marian163/proiect_tsc/Hardware/Schematic_PCB.sch

## EAGLE design Hardware/Schematic_PCB.sch (2026-04-19)

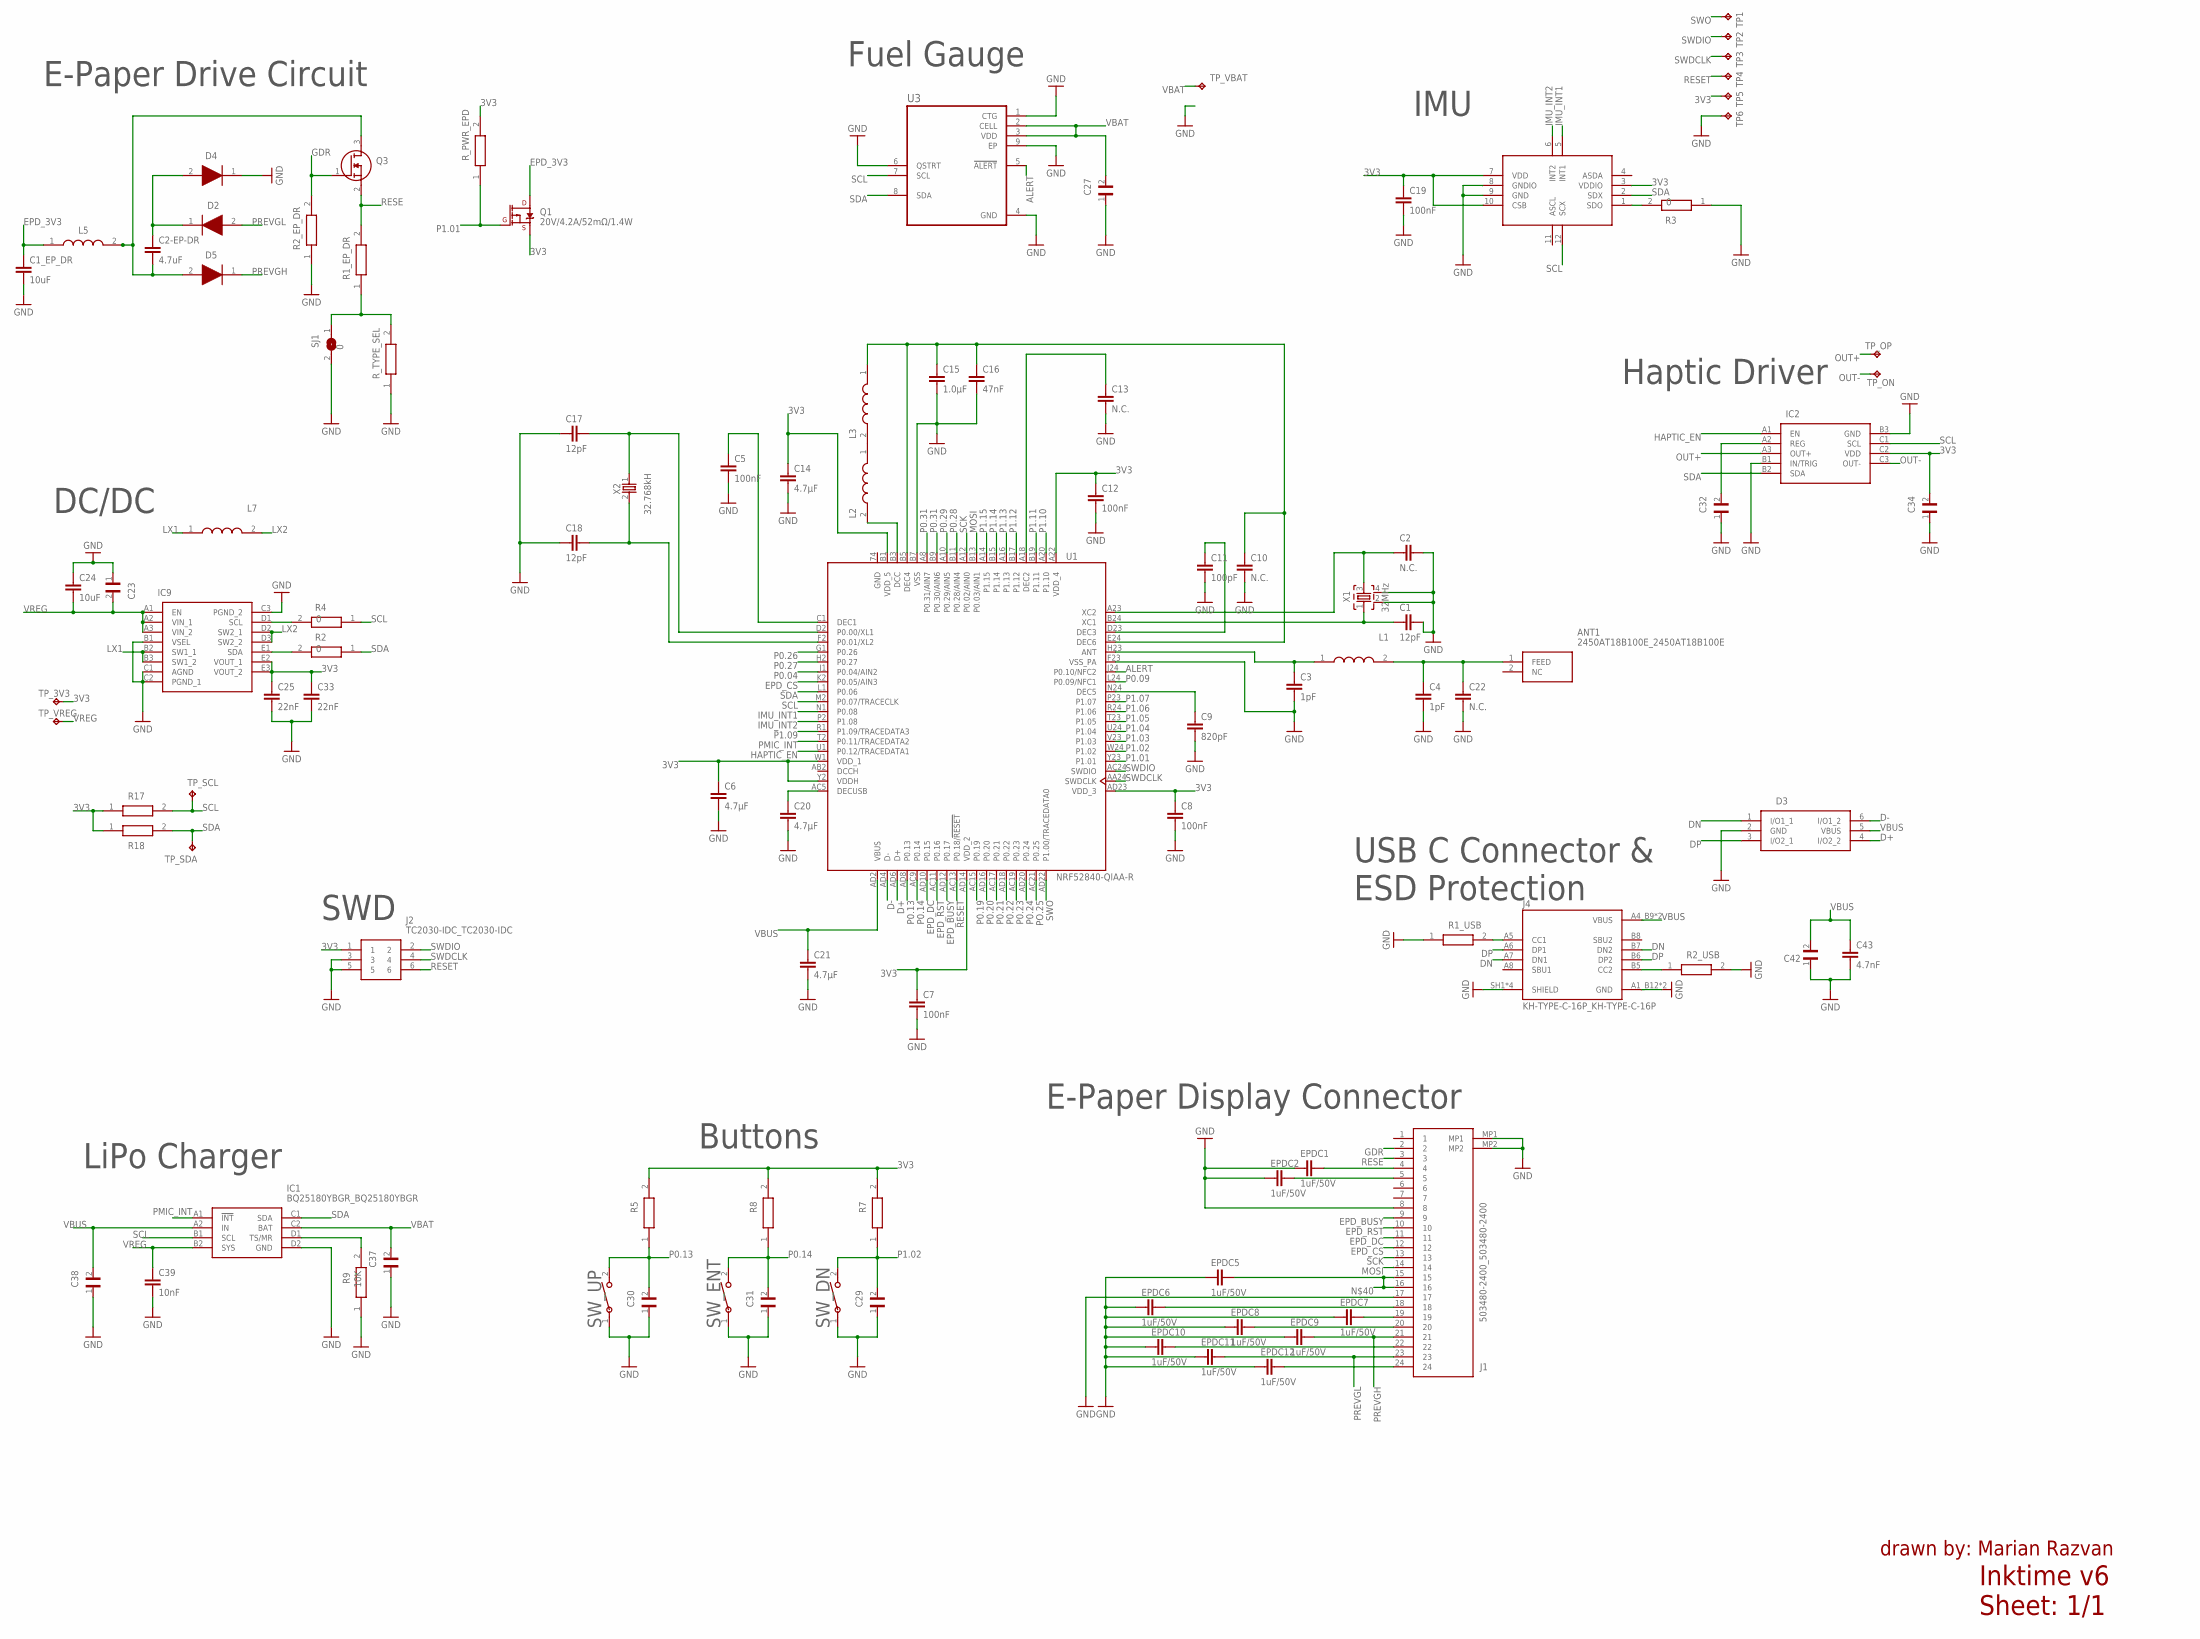
[picture p6: schematic Schematic_PCB.sch, sheet 1]

Parts:
ANT1: 2450AT18B100E_2450AT18B100E; 2450AT18B100E_ANTC3216X140N
C1, C17, C18: 12pF; NORDIC_NRF_3_RESC0201_L
C1_EP_DR, C24: 10uF; NORDIC_NRF_3_RESC0201_L
C2, C10, C13, C22: N.C.; NORDIC_NRF_3_RESC0201_L
C2-EP-DR: 4.7uF; ESP32_C6_LIBRARY_1_ESP32_WROVER_EAGLE-LTSPICE_C0402
C3, C4: 1pF; NORDIC_NRF_3_RESC0201_L
C5, C7, C8, C12, C19: 100nF; NORDIC_NRF_3_RESC0201_L
C6, C14, C20, C21: 4.7µF; ESP32_C6_LIBRARY_1_ESP32_WROVER_EAGLE-LTSPICE_C0402
C9: 820pF; NORDIC_NRF_3_RESC0201_L
C11: 100pF; NORDIC_NRF_3_RESC0201_L
C15: 1.0µF; ESP32_C6_LIBRARY_1_ESP32_WROVER_EAGLE-LTSPICE_C0402
C16: 47nF; ESP32_C6_LIBRARY_1_ESP32_WROVER_EAGLE-LTSPICE_C0402
C23, C27, C42: 0.1uF; GRM011R60J152KE01L_2_CAPC0201X13N
C25, C33: 22nF; NORDIC_NRF_3_RESC0201_L
C29, C30, C31, C32, C37, C38: 1uF; GRM011R60J152KE01L_2_CAPC0201X13N
C34: 01.uF; GRM011R60J152KE01L_2_CAPC0201X13N
C39: 10nF; NORDIC_NRF_3_RESC0201_L
C43: 4.7nF; NORDIC_NRF_3_RESC0201_L
D2, D4, D5: ESP32_C6_LIBRARY_5_MBR0530; ESP32_C6_LIBRARY_5_SOD3716X135N
D3: ESP32_C6_LIBRARY_3_USBLC6-2SC6Y; ESP32_C6_LIBRARY_3_SOT95P280X145-6N
EPDC1, EPDC2, EPDC5, EPDC6, EPDC7, EPDC8, EPDC9, EPDC10, EPDC11, EPDC12: 1uF/50V; NORDIC_NRF_3_RESC0201_L
IC1: BQ25180YBGR_BQ25180YBGR; BQ25180YBGR_BGA8C40P2X4_100X155X50
IC2: DRV2605YZFR_DRV2605YZFR; DRV2605YZFR_BGA9C50P3X3_144X144X62
IC3: BMA423_BMA423
IC9: RT6160AWSC_RT6160AWSC; RT6160AWSC_BGA15C40P3X5_140X230X60
J1: 503480-2400_503480-2400; 503480-2400_5034802400
J2: TC2030-IDC_TC2030-IDC; TC2030-IDC_TC2030IDC
J4: KH-TYPE-C-16P_KH-TYPE-C-16P; KH-TYPE-C-16P_KINGHELM_KH-TYPE-C-16P
L1, L7: MLP2016SR47MT0S1_FTC252012SR47MBCA; MLP2016SR47MT0S1_INDC2016X100N
L2: 10µH; MLP2016SR47MT0S1_INDC2016X100N
L3: 15nH; MLP2016SR47MT0S1_INDC2016X100N
L5: 68uH; MLP2016SR47MT0S1_INDC2016X100N
Q1: 20V/4.2A/52mΩ/1.4W; ESP32_C6_LIBRARY_4_ESP32_C6_LIBRARY_4_ESP32_C6_LIBRARY_4_ES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
Q3: ESP32_C6_LIBRARY_6_SI1308EDL-T1-GE3; ESP32_C6_LIBRARY_6_SOT65P210X110-3N
R1_EP_DR: 0.47; ERA-1AEB3401C_0201
R1_USB, R2_USB: 5K1; ERA-1AEB3401C_0201
R2, R3, R4: 0; ERA-1AEB3401C_0201
R2_EP_DR, R5, R7, R8, R9: 10K; ERA-1AEB3401C_0201
R17, R18: ERA-1AEB3401C_CPF0201D7K68C1; ERA-1AEB3401C_0201
R_PWR_EPD: 10K; ERA-1AEB3401C_0201
R_TYPE_SEL: 2.2; ERA-1AEB3401C_0201
SJ1: 0; ESP32_C6_LIBRARY_7_JUMPER_SJ
SW_DN: 2025-10-22_07-23-44_LIBRARY_EVP-AKE31ASW_EVP-AKE3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; 2025-10-22_07-23-44_LIBRARY_SW_EVP-AKE31A_PAN
SW_ENT: 2025-10-22_07-23-44_LIBRARY_EVP-AKE31ASW_EVP-AKE3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; 2025-10-22_07-23-44_LIBRARY_SW_EVP-AKE31A_PAN
SW_UP: 2025-10-22_07-23-44_LIBRARY_EVP-AKE31ASW_EVP-AKE3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; 2025-10-22_07-23-44_LIBRARY_SW_EVP-AKE31A_PAN
TP1, TP2, TP3, TP4, TP5, TP6: HECTOR_WATCH_1_TPTP20R; HECTOR_WATCH_1_TP20R
TP_3V3: HECTOR_WATCH_1_TPTP20R; HECTOR_WATCH_1_TP20R
TP_ON: HECTOR_WATCH_1_TPTP20R; HECTOR_WATCH_1_TP20R
TP_OP: HECTOR_WATCH_1_TPTP20R; HECTOR_WATCH_1_TP20R
TP_SCL: HECTOR_WATCH_1_TPTP20R; HECTOR_WATCH_1_TP20R
TP_SDA: HECTOR_WATCH_1_TPTP20R; HECTOR_WATCH_1_TP20R
TP_VBAT: HECTOR_WATCH_1_TPTP20R; HECTOR_WATCH_1_TP20R
TP_VREG: HECTOR_WATCH_1_TPTP20R; HECTOR_WATCH_1_TP20R
U1: NRF52840-QIAA-R; NRF52840-QIAA
U3: ESP32_C6_LIBRARY_MAX17048G+T10; ESP32_C6_LIBRARY_SON50P200X200X80-9N
X1: 32MHz; NORDIC_NRF_BT-XTAL_2016_N
X2: 32.768kH; NORDIC_NRF_1_XTAL_3215_N

Connections:
3V3: C6.1, C7.1, C8.1, C12.1, C14.1, C19.1, C25.1, C33.1, C34.2, IC2.C2 (VDD), IC3.3 (VDDIO), IC3.7 (VDD), IC3.10 (CSB), IC9.E2 (VOUT_1), IC9.E3 (VOUT_2), J2.1, Q1.2 (S), R5.2, R7.2, R8.2, R17.1, R18.1, R_PWR_EPD.2, TP5.TP, TP_3V3.TP, U1.A22 (VDD_4), U1.AD14 (VDD_2), U1.AD23 (VDD_3), U1.B1 (VDD_5), U1.W1 (VDD_1), U1.Y2 (VDDH)
ALERT: U1.J24 (P0.10/NFC2), U3.5 (!ALERT)
D+: D3.4 (I/O2_2), U1.AD6 (D+)
D-: D3.6 (I/O1_2), U1.AD4 (D-)
DN: D3.1 (I/O1_1), J4.A7 (DN1), J4.B7 (DN2)
DP: D3.3 (I/O2_1), J4.A6 (DP1), J4.B6 (DP2)
EPD_3V3: C1_EP_DR.1, L5.1, Q1.3 (D)
EPD_BUSY: J1.9, U1.AD12 (P0.17)
EPD_CS: J1.12, U1.K2 (P0.05/AIN3)
EPD_DC: J1.11, U1.AD10 (P0.15)
EPD_RST: J1.10, U1.AC11 (P0.16)
GDR: J1.2, Q3.1 (G), R2_EP_DR.2
GND: C1.2, C1_EP_DR.2, C2.2, C3.2, C4.2, C5.2, C6.2, C7.2, C8.2, C9.2, C10.2, C11.2, C12.2, C13.2, C14.2, C15.2, C16.2, C17.1, C18.1, C19.2, C20.2, C21.2, C22.2, C23.1, C24.1, C25.2, C27.1, C29.1, C30.1, C31.1, C32.1, C33.2, C34.1, C37.1, C38.1, C39.2, C42.1, C43.2, D3.2 (GND), D4.1 (K), EPDC1.1, EPDC2.1, EPDC5.1, EPDC6.1, EPDC7.1, EPDC8.1, EPDC9.1, EPDC10.1, EPDC11.1, EPDC12.1, IC1.D2 (GND), IC2.B1 (IN/TRIG), IC2.B3 (GND), IC3.8 (GNDIO), IC3.9 (GND), IC9.B1 (VSEL), IC9.C1 (AGND), IC9.C2 (PGND_1), IC9.C3 (PGND_2), J1.8, J1.17, J1.MP1, J1.MP2, J2.3, J2.5, J4.A1_B12 (GND), J4.SH1 (SHIELD), R1_USB.1, R2_EP_DR.1, R2_USB.2, R3.1, R9.1, R_TYPE_SEL.1, SJ1.2, SW_DN.1, SW_ENT.1, SW_UP.1, TP6.TP, U1.B7 (VSS), U1.F23 (VSS_PA), U3.1 (CTG), U3.4 (GND), U3.6 (QSTRT), U3.9 (EP), X1.2, X1.4
HAPTIC_EN: IC2.A1 (EN), U1.U1 (P0.12/TRACEDATA1)
IMU_INT1: IC3.5 (INT1), U1.N1 (P0.08)
IMU_INT2: IC3.6 (INT2), U1.P2 (P1.08)
LX1: IC9.B2 (SW1_1), IC9.B3 (SW1_2), L7.1
LX2: IC9.D2 (SW2_1), IC9.D3 (SW2_2), L7.2
MOSI: J1.14, U1.B13 (P0.03/AIN1)
unnamed: IC1.D1 (TS/MR), R9.2
unnamed: IC9.D1 (SCL), R4.2
unnamed: IC9.E1 (SDA), R2.2
unnamed: L2.1, L3.2
unnamed: L2.2, U1.B3 (DCC)
unnamed: C5.1, U1.C1 (DEC1)
unnamed: C10.1, C15.1, C16.1, L3.1, U1.B5 (DEC4), U1.E24 (DEC6)
unnamed: C17.2, U1.D2 (P0.00/XL1), X2.1
unnamed: C13.1, U1.A18 (DEC2)
unnamed: IC3.1 (SDO), R3.2
unnamed: C18.2, U1.F2 (P0.01/XL2), X2.2
unnamed: C11.1, U1.D23 (DEC3)
unnamed: C20.1, U1.AC5 (DECUSB)
unnamed: C1.1, U1.B24 (XC1), X1.1
unnamed: C2.1, U1.A23 (XC2), X1.3
unnamed: C32.2, IC2.A2 (REG)
unnamed: C3.1, L1.1, U1.H23 (ANT)
unnamed: ANT1.1 (FEED), C4.1, C22.1, L1.2
unnamed: C9.1, U1.N24 (DEC5)
unnamed: C2-EP-DR.1, D2.1 (K), D4.2 (A)
unnamed: C2-EP-DR.2, D5.2 (A), L5.2, Q3.3 (D)
unnamed: EPDC1.2, J1.4
unnamed: J4.A5 (CC1), R1_USB.2
unnamed: R1_EP_DR.1, R_TYPE_SEL.2, SJ1.1
unnamed: J4.B5 (CC2), R2_USB.1
unnamed: EPDC2.2, J1.5
unnamed: EPDC5.2, J1.15, J1.16
unnamed: EPDC6.2, J1.18
unnamed: EPDC7.2, J1.19
unnamed: EPDC8.2, J1.20
unnamed: EPDC10.2, J1.22
unnamed: EPDC12.2, J1.24
OUT+: IC2.A3 (OUT+), TP_OP.TP
OUT-: IC2.C3 (OUT-), TP_ON.TP
P0.04: U1.J1 (P0.04/AIN2)
P0.09: U1.L24 (P0.09/NFC1)
P0.13: C30.2, R5.1, SW_UP.2, U1.AD8 (P0.13)
P0.14: C31.2, R8.1, SW_ENT.2, U1.AC9 (P0.14)
P0.19: U1.AC15 (P0.19)
P0.20: U1.AD16 (P0.20)
P0.21: U1.AC17 (P0.21)
P0.22: U1.AD18 (P0.22)
P0.23: U1.AC19 (P0.23)
P0.24: U1.AD20 (P0.24)
P0.26: U1.G1 (P0.26)
P0.27: U1.H2 (P0.27)
P0.28: U1.B11 (P0.28/AIN4)
P0.29: U1.A10 (P0.29/AIN5)
P0.31: U1.A8 (P0.31/AIN7), U1.B9 (P0.30/AIN6)
P1.01: Q1.1 (G), R_PWR_EPD.1, U1.Y23 (P1.01)
P1.02: C29.2, R7.1, SW_DN.2, U1.W24 (P1.02)
P1.03: U1.V23 (P1.03)
P1.04: U1.U24 (P1.04)
P1.05: U1.T23 (P1.05)
P1.06: U1.R24 (P1.06)
P1.07: U1.P23 (P1.07)
P1.09: U1.R1 (P1.09/TRACEDATA3)
P1.10: U1.A20 (P1.10)
P1.11: U1.B19 (P1.11)
P1.12: U1.B17 (P1.12)
P1.13: U1.B15 (P1.14)
P1.14: U1.A16 (P1.13)
P1.15: U1.A14 (P1.15)
PMIC_INT: IC1.A1 (!INT), U1.T2 (P0.11/TRACEDATA2)
PO.25: U1.AC21 (P0.25)
PREVGH: D5.1 (K), EPDC9.2, J1.21
PREVGL: D2.2 (A), EPDC11.2, J1.23
RESE: J1.3, Q3.2 (S), R1_EP_DR.2
RESET: J2.6, TP4.TP, U1.AC13 (P0.18/!RESET)
SCK: J1.13, U1.A12 (P0.02/AIN0)
SCL: IC1.B1 (SCL), IC2.C1 (SCL), IC3.12 (SCX), R4.1, R17.2, TP_SCL.TP, U1.M2 (P0.07/TRACECLK), U3.7 (SCL)
SDA: IC1.C1 (SDA), IC2.B2 (SDA), IC3.2 (SDX), R2.1, R18.2, TP_SDA.TP, U1.L1 (P0.06), U3.8 (SDA)
SWDCLK: J2.4, TP3.TP, U1.AA24 (SWDCLK)
SWDIO: J2.2, TP2.TP, U1.AC24 (SWDIO)
SWO: TP1.TP, U1.AD22 (P1.00/TRACEDATA0)
VBAT: C27.2, C37.2, IC1.C2 (BAT), TP_VBAT.TP, U3.2 (CELL), U3.3 (VDD)
VBUS: C21.1, C38.2, C42.2, C43.1, D3.5 (VBUS), IC1.A2 (IN), J4.A4_B9 (VBUS), U1.AD2 (VBUS)
VREG: C23.2, C24.2, C39.1, IC1.B2 (SYS), IC9.A1 (EN), IC9.A2 (VIN_1), IC9.A3 (VIN_2), TP_VREG.TP

Notes on the sheet:
E-Paper Drive Circuit
Haptic Driver
Buttons
USB C Connector & ESD Protection
LiPo Charger
DC/DC
IMU
Fuel Gauge
SWD
E-Paper Display Connector
Inktime v6
Sheet: 1/1
drawn by: Marian Razvan
